ochin-space/ochin-CM4v2/3d/ochin VRX goggleBox/kicad RTL8812AU module pwr/RTL8812AU.png

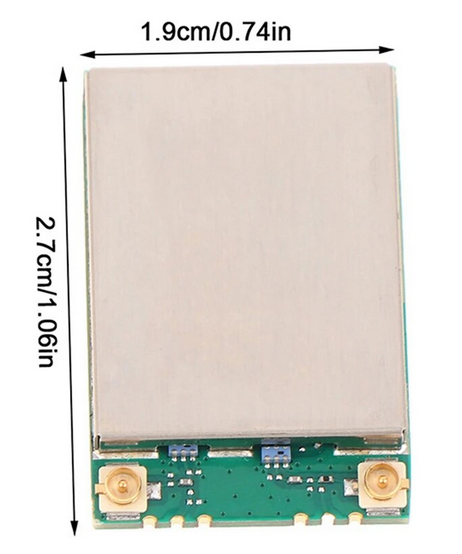
3d/ochin VRX goggleBox/kicad RTL8812AU module pwr/RTL8812AU.png
