ochin-space/ochin-CM4v2/images/IMG_20230827_133044.jpg

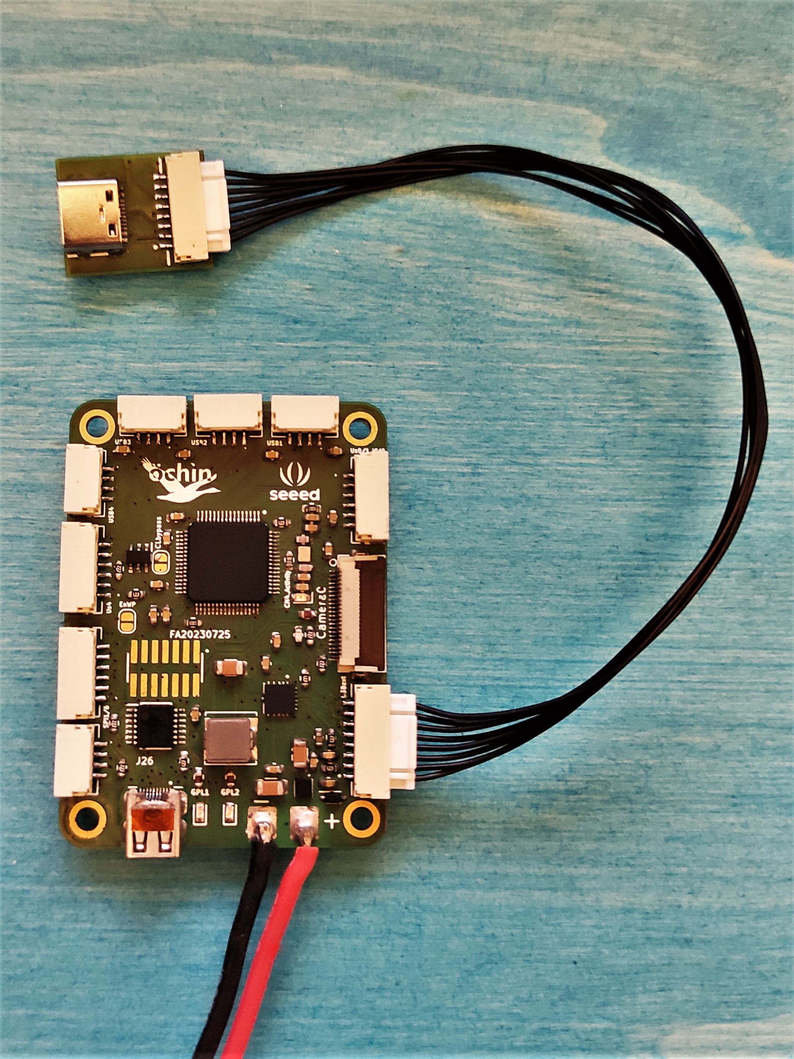
images/IMG_20230827_133044.jpg
