ochin-space/ochin-CM4v2/images/Ochin_CM4_bot_main.png

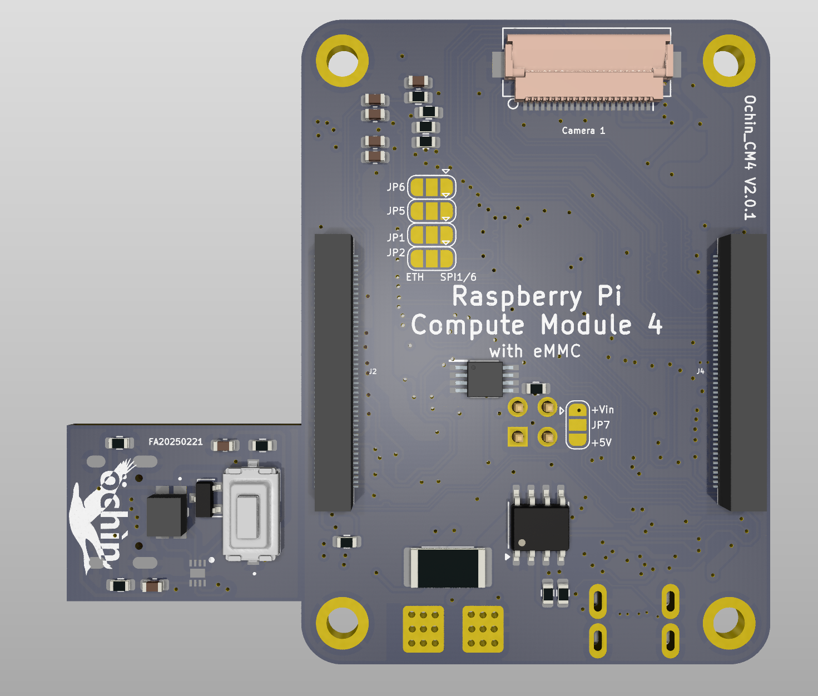
images/Ochin_CM4_bot_main.png
