ochin-space/ochin-CM4v2/3d/CoversTurretsAndExtractors/ochin_mount-extractor.stl

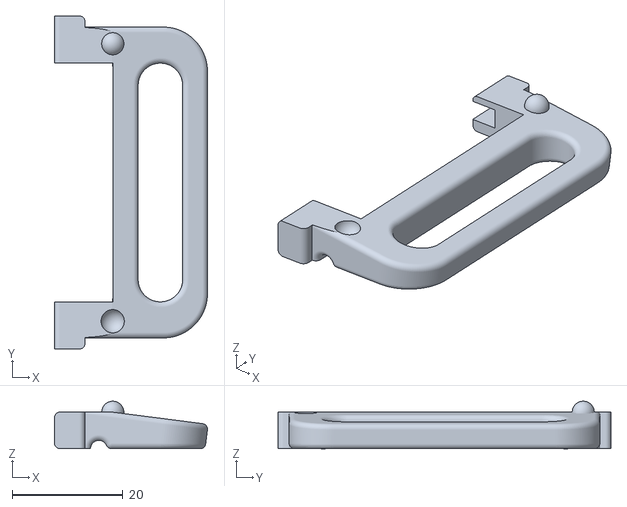
[picture p28: CAD file, 2023-08-27]
3d/CoversTurretsAndExtractors/ochin_mount-extractor.stl
27.6 x 60.0 x 8.58
