ochin-space/ochin-CM4v2/3d/ochin VRX goggleBox/kicad RTL8812AU module pwr/RTL8812AU_module/RTL8812AU_module.pdf

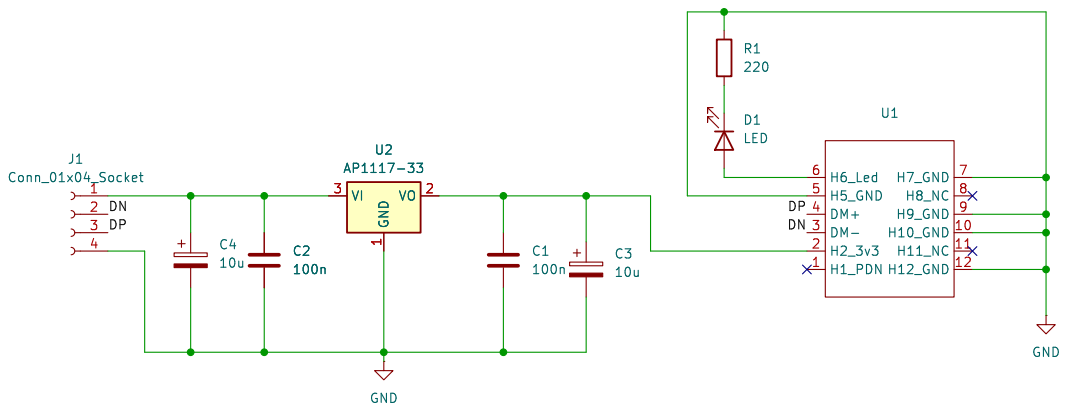
[picture p89: page 1]

Id: 1/1 Title: File: RTL8812AU_module.kicad_sch Sheet: / GND
